pierre-muth/c-zero_dashboard/image1.jpg

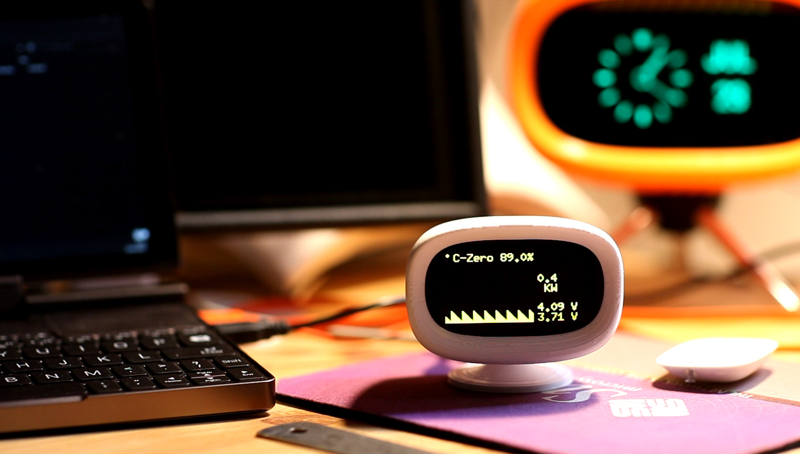
image1.jpg
