pierre-muth/c-zero_dashboard/picture_shematics/IMG_20220814_121153.jpg

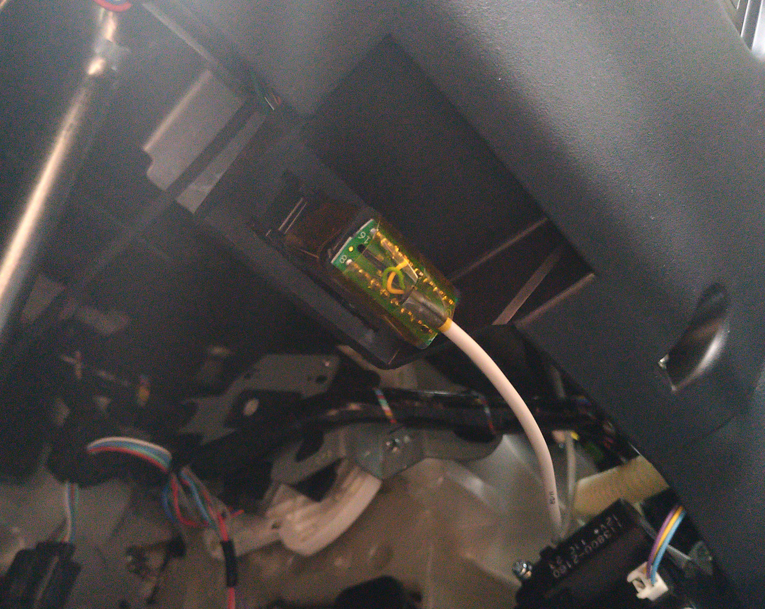
picture_shematics/IMG_20220814_121153.jpg
