pierre-muth/c-zero_dashboard/picture_shematics/IMG_20220814_122057.jpg

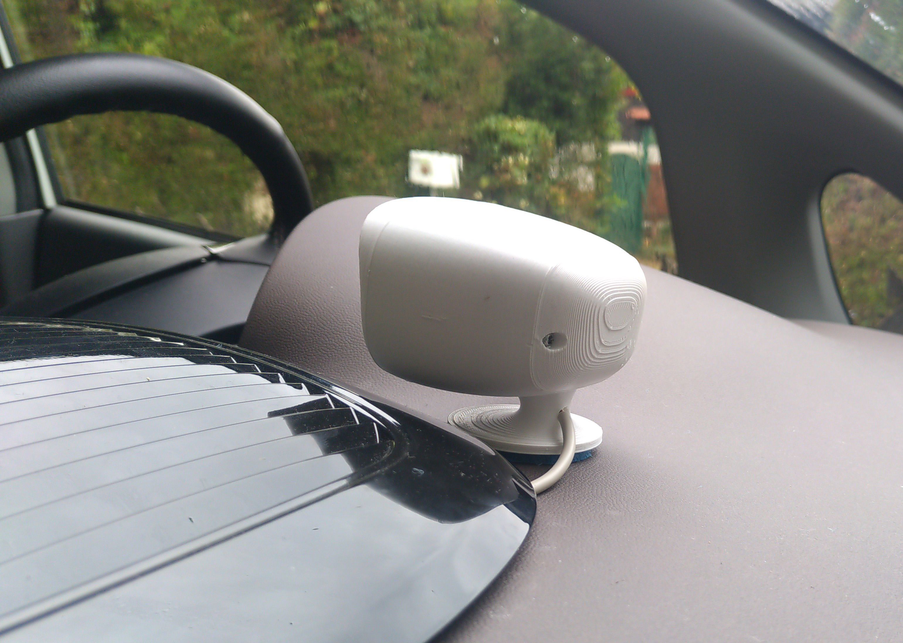
picture_shematics/IMG_20220814_122057.jpg
